ceybers/shifty-split-keyboard/images/sketches/IMG_20231126_144634.jpg

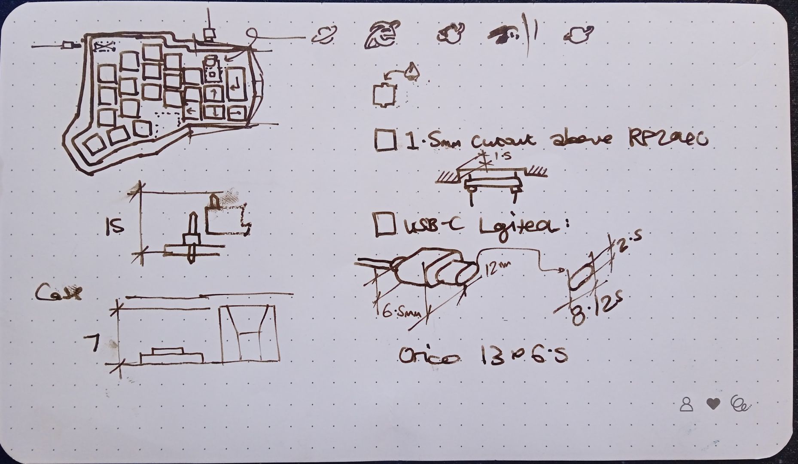
images/sketches/IMG_20231126_144634.jpg
